ENACRobotique/2021_Robot_B/base/src/stateMachine/AbstractState.h

/*
 * AbstractState.h
 *
 *  Created on: 11 avr. 2018
 *      Author: robot
 */

#ifndef STATEMACHINE_ABSTRACTSTATE_H_
#define STATEMACHINE_ABSTRACTSTATE_H_


class AbstractState {
public:
	AbstractState();
	virtual ~AbstractState() {};

	virtual void enter() = 0;
	virtual void doIt() = 0;
	virtual void leave() = 0;
	virtual void reEnter(unsigned long InterruptTime) {}
	virtual void forceLeave() {}
	virtual void pauseNextState() {}

	unsigned long getFlags() const {
		return flags;
	}

	void setFlags(unsigned long flags) {
		this->flags = flags;
	}
	//String name = String();
	//^^^^ Laisser commenterpour pouvoir debugger du code en local sans passer par la librarie arduino


protected:
	unsigned long flags;
	//unsigned long time_start;
};

#endif /* STATEMACHINE_ABSTRACTSTATE_H_ */
