ENACRobotique/2021_Robot_B/base/src/FsmSupervisor.h

/*
 * FsmSupervisor.h
 *
 *  Created on: 11 avr. 2018
 *      Author: robot
 */

#ifndef STATEMACHINE_FsmSupervisor_H_
#define STATEMACHINE_FsmSupervisor_H_

#include "./stateMachine/AbstractState.h"

class FsmSupervisor {
public:
	FsmSupervisor();
	virtual ~FsmSupervisor();
	void setNextState(AbstractState* state);
	void update();
	void init();
	//AbstractState& get_current_state();
	//void print_State();
	//String get_current_state();
	bool is_no_state_set();
	bool is_switching_state();

private:

	//void update_state();
	AbstractState* nextState;
	AbstractState* currentState;
	AbstractState* previousState;
	unsigned long time_obstacle_left;
	bool isSwitchingState; //true if setNextState is called but update hasn't been called (which means that currentState != nextState at the moment)
};

extern FsmSupervisor fsmSupervisor;

#endif /* STATEMACHINE_FsmSupervisor_H_ */
