ENACRobotique/2021_Robot_B/base/src/stateMachine/DeployPavillon.h

#pragma once 
#include <Arduino.h>
#include "AbstractState.h"

class DeployPavillon : public AbstractState {
public:
	DeployPavillon();

	void enter();
	void doIt();
	void leave();
protected:
    unsigned long time_start;
};

extern DeployPavillon deployPavillon;
