ENACRobotique/2021_Robot_B/base/src/examples/asservissementMoteur.cpp

#include "asservissementMoteur.h"
#include "../motorControl.h"
#include "../navigator.h"

#include "Metro.h"
#include "../params.h"

float cons_test[5] = {0.f, 3.f, 0.f, 3.f, 0.f };


namespace asservissementMoteur {
    int i = 0;
    void update()
    {
        SerialDebug.println(i);
        i = (i==4) ? 0 : i+1;
            navigator.move(0, cons_test[i]);
            //MotorControl::set_cons(cons_test[i], 0);

    }



}
